GenniImparato/Digital_Audio_Effect/firmware/source/config.h

#ifndef 			CONFIGURATION_FILE_H
#define 			CONFIGURATION_FILE_H

#define 			AUDIO_BUFFERS_SIZE			512
#define				AUDIO_SAMPLING_FREQUENCY	44100.0

#define				POTS_COUNT					4


typedef				miosix::BufferQueue<unsigned short,AUDIO_BUFFERS_SIZE>		AudioBufferQueue;

#endif
