GenniImparato/Digital_Audio_Effect/firmware/source/LedMatrix_Driver/Leds_Chars.h

#ifndef LEDS_CHARS___
#define LEDS_CHARS___

#include "LedMatrix_Driver.h"

LedChar A {
{0, 1, 0},
{1, 0, 1},
{1, 1, 1},
{1, 0, 1},
{1, 0, 1},
};

LedChar B {
{1, 1, 0},
{1, 0, 1},
{1, 1, 0},
{1, 0, 1},
{1, 1, 0},
};

LedChar C {
{0, 1, 1},
{1, 0, 0},
{1, 0, 0},
{1, 0, 0},
{0, 1, 1},
};

LedChar D {
{1, 1, 0},
{1, 0, 1},
{1, 0, 1},
{1, 0, 1},
{1, 1, 0},
};

LedChar E {
{1, 1, 1},
{1, 0, 0},
{1, 1, 1},
{1, 0, 0},
{1, 1, 1},
};

LedChar F {
{1, 1, 1},
{1, 0, 0},
{1, 1, 1},
{1, 0, 0},
{1, 0, 0},
};

LedChar G {
{0, 1, 1},
{1, 0, 0},
{1, 1, 1},
{1, 0, 1},
{0, 1, 1},
};

LedChar H {
{1, 0, 1},
{1, 0, 1},
{1, 1, 1},
{1, 0, 1},
{1, 0, 1},
};

LedChar I {
{0, 1, 0},
{0, 1, 0},
{0, 1, 0},
{0, 1, 0},
{0, 1, 0},
};

LedChar J {
{0, 0, 1},
{0, 0, 1},
{0, 0, 1},
{0, 0, 1},
{1, 1, 1},
};

LedChar K {
{1, 0, 1},
{1, 1, 0},
{1, 0, 0},
{1, 1, 0},
{1, 0, 1},
};

LedChar L {
{1, 0, 0},
{1, 0, 0},
{1, 0, 0},
{1, 0, 0},
{1, 1, 1},
};

LedChar M {
{1, 0, 1},
{1, 1, 1},
{1, 0, 1},
{1, 0, 1},
{1, 0, 1},
};

LedChar N {
{1, 0, 1},
{1, 0, 1},
{1, 1, 1},
{1, 0, 1},
{1, 0, 1},
};

LedChar O {
{0, 1, 0},
{1, 0, 1},
{1, 0, 1},
{1, 0, 1},
{0, 1, 0},
};

LedChar P {
{1, 1, 1},
{1, 0, 1},
{1, 1, 1},
{1, 0, 0},
{1, 0, 0},
};

LedChar Q {
{1, 1, 1},
{1, 0, 1},
{1, 1, 1},
{1, 1, 0},
{0, 0, 1},
};

LedChar R {
{1, 1, 1},
{1, 0, 1},
{1, 1, 0},
{1, 0, 1},
{1, 0, 1},
};

LedChar S {
{0, 1, 1},
{1, 0, 0},
{1, 1, 1},
{0, 0, 1},
{1, 1, 0},
};

LedChar T {
{1, 1, 1},
{0, 1, 0},
{0, 1, 0},
{0, 1, 0},
{0, 1, 0},
};

LedChar U {
{1, 0, 1},
{1, 0, 1},
{1, 0, 1},
{1, 0, 1},
{1, 1, 1},
};

LedChar V {
{1, 0, 1},
{1, 0, 1},
{1, 0, 1},
{1, 0, 1},
{0, 1, 0},
};

LedChar W {
{1, 0, 1},
{1, 0, 1},
{1, 1, 1},
{1, 1, 1},
{1, 1, 1},
};

LedChar X {
{1, 0, 1},
{1, 0, 1},
{0, 1, 0},
{1, 0, 1},
{1, 0, 1},
};

LedChar Y {
{1, 0, 1},
{1, 0, 1},
{0, 1, 0},
{0, 1, 0},
{0, 1, 0},
};

LedChar Z {
{1, 1, 1},
{0, 0, 1},
{0, 1, 0},
{1, 0, 0},
{1, 1, 1},
};

LedChar ZERO {
{1, 1, 1},
{1, 0, 1},
{1, 0, 1},
{1, 0, 1},
{1, 1, 1},
};

LedChar ONE {
{0, 1, 0},
{1, 1, 0},
{0, 1, 0},
{0, 1, 0},
{1, 1, 1},
};

LedChar TWO {
{1, 1, 1},
{0, 0, 1},
{1, 1, 1},
{1, 0, 0},
{1, 1, 1},
};

LedChar THREE {
{1, 1, 1},
{0, 0, 1},
{1, 1, 1},
{0, 0, 1},
{1, 1, 1},
};

LedChar FOUR {
{1, 0, 1},
{1, 0, 1},
{1, 1, 1},
{0, 0, 1},
{0, 0, 1},
};

LedChar FIVE {
{1, 1, 1},
{1, 0, 0},
{1, 1, 1},
{0, 0, 1},
{1, 1, 1},
};

LedChar SIX {
{1, 1, 1},
{1, 0, 0},
{1, 1, 1},
{1, 0, 1},
{1, 1, 1},
};

LedChar SEVEN {
{1, 1, 1},
{0, 0, 1},
{0, 0, 1},
{0, 0, 1},
{0, 0, 1},
};

LedChar EIGHT {
{1, 1, 1},
{1, 0, 1},
{1, 1, 1},
{1, 0, 1},
{1, 1, 1},
};

LedChar NINE {
{1, 1, 1},
{1, 0, 1},
{1, 1, 1},
{0, 0, 1},
{1, 1, 1},
};

LedChar POINT {
{0, 0, 0},
{0, 0, 0},
{0, 0, 0},
{0, 0, 0},
{0, 1, 0},
};

LedChar SPACE {
{0, 0, 0},
{0, 0, 0},
{0, 0, 0},
{0, 0, 0},
{0, 0, 0},
};

#endif
