GenniImparato/Digital_Audio_Effect/firmware/source/ADC_Driver/Filter.h

template <uint8_t N, class input_t = unsigned short, class sum_t = unsigned int>
class ADCFilter {
  public:
    input_t operator()(input_t input) {
        sum -= previousInputs[index];
        sum += input;
        previousInputs[index] = input;
        if (++index == N)
            index = 0;
        return (sum + (N / 2)) / N;
    }
    
    static_assert(
        sum_t(0) < sum_t(-1),  // Check that `sum_t` is an unsigned type
        "Error: sum data type should be an unsigned integer, otherwise, "
        "the rounding operation in the return statement is invalid.");

  private:
    uint8_t index             = 0;
    input_t previousInputs[N] = {};
    sum_t sum                 = 0;
};
