GenniImparato/Digital_Audio_Effect/firmware/source/utils.cpp

int map(int x, int in_min, int in_max, int out_min, int out_max)
{
  return (x - in_min) * (out_max - out_min) / (in_max - in_min) + out_min;
}

float map_f(float x, float in_min, float in_max, float out_min, float out_max)
{
  return (x - in_min) * (out_max - out_min) / (in_max - in_min) + out_min;
}
